jviktes/Astrograf/3DPrint/Modular_planetary_gearbox__1024/images/3fe68c79d25a81dcb26cbcb582fad782_preview_featured.jpg

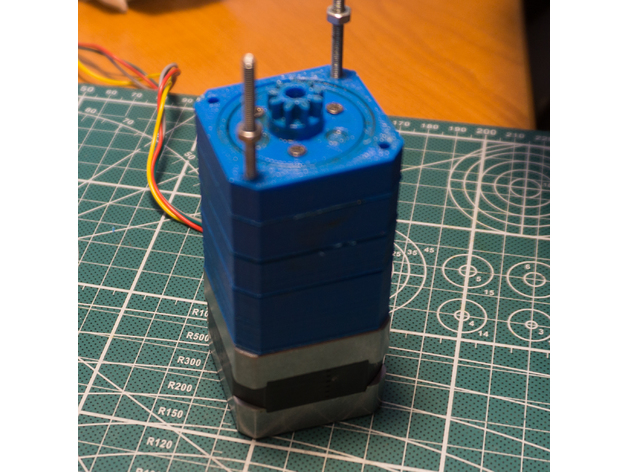
3DPrint/Modular_planetary_gearbox__1024/images/3fe68c79d25a81dcb26cbcb582fad782_preview_featured.jpg
