jviktes/Astrograf/3DPrint/Modular_planetary_gearbox__1024/images/6f2f0f552271744cae626b99cfb380dd_preview_featured.jpg

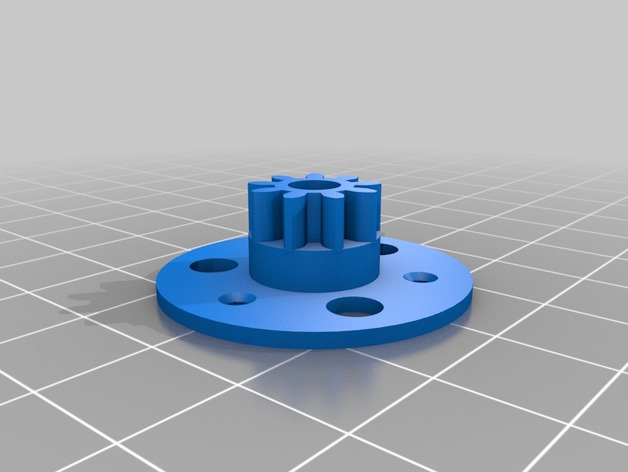
3DPrint/Modular_planetary_gearbox__1024/images/6f2f0f552271744cae626b99cfb380dd_preview_featured.jpg
