jviktes/Astrograf/3DPrint/Modular_planetary_gearbox__1024/images/7bb7e70e9617966f21e6dd5f7fba5066_preview_featured.jpg

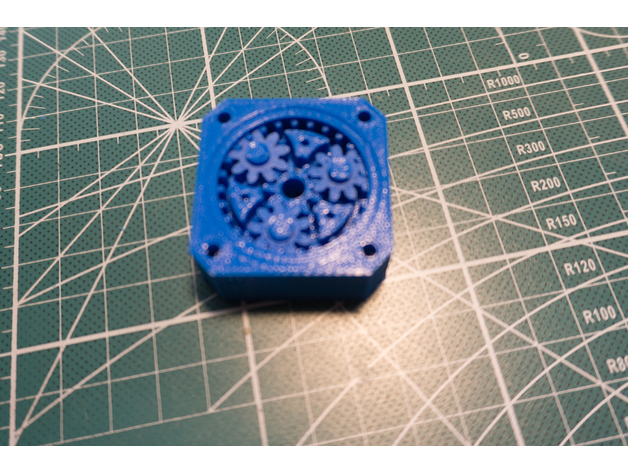
3DPrint/Modular_planetary_gearbox__1024/images/7bb7e70e9617966f21e6dd5f7fba5066_preview_featured.jpg
