jviktes/Astrograf/3DPrint/Modular_planetary_gearbox__1024/images/9a64f82b3e09b2cae3e578f5d89d99b6_preview_featured.jpg

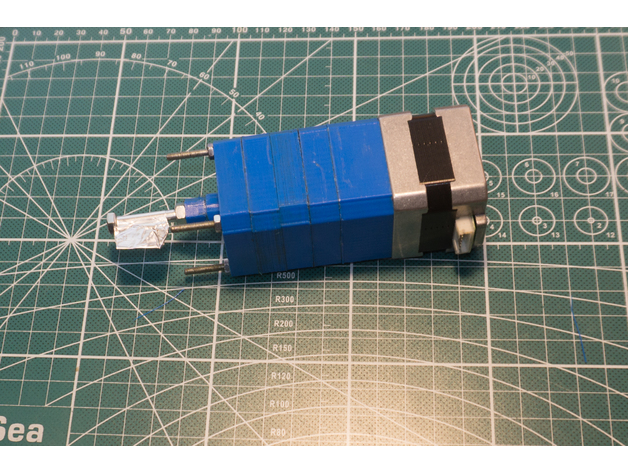
3DPrint/Modular_planetary_gearbox__1024/images/9a64f82b3e09b2cae3e578f5d89d99b6_preview_featured.jpg
