jviktes/Astrograf/3DPrint/Modular_planetary_gearbox__1024/images/9c8101880a9e5dfc09dd12966d4b34e6_preview_featured.jpg

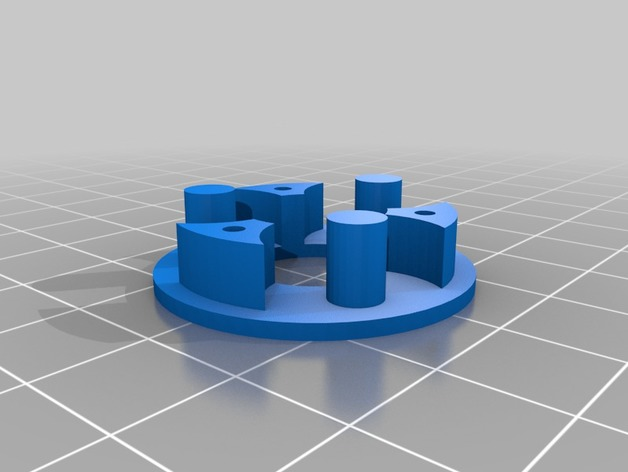
3DPrint/Modular_planetary_gearbox__1024/images/9c8101880a9e5dfc09dd12966d4b34e6_preview_featured.jpg
