jviktes/Astrograf/3DPrint/Modular_planetary_gearbox__1024/images/43a152fd7e8cf67ea3baf1d21f4f2fe9_preview_featured.jpg

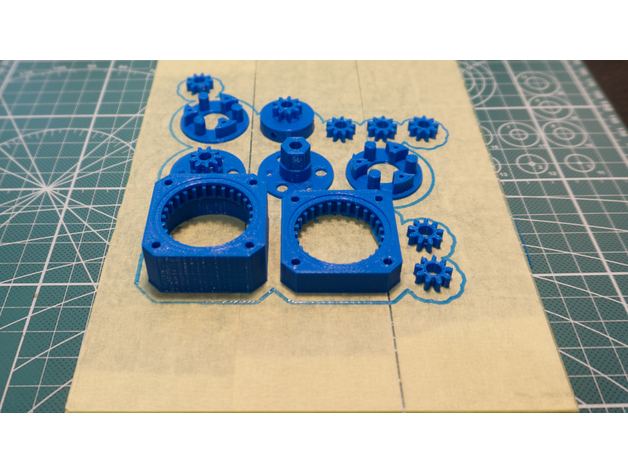
3DPrint/Modular_planetary_gearbox__1024/images/43a152fd7e8cf67ea3baf1d21f4f2fe9_preview_featured.jpg
