jviktes/Astrograf/3DPrint/Modular_planetary_gearbox__1024/images/76d2ecaf834df607a9b20ee27e41b75c_preview_featured.jpg

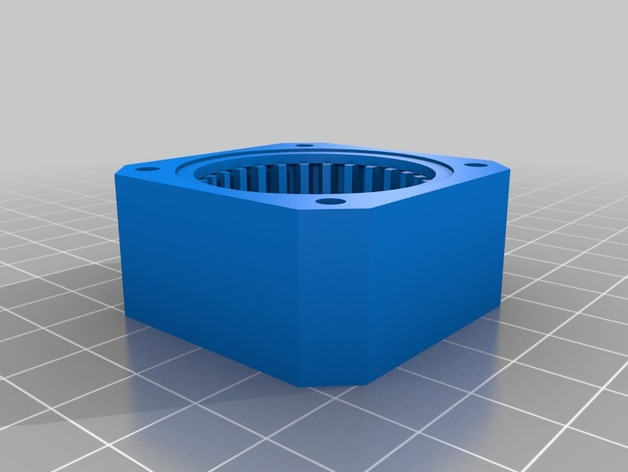
3DPrint/Modular_planetary_gearbox__1024/images/76d2ecaf834df607a9b20ee27e41b75c_preview_featured.jpg
