jviktes/Astrograf/3DPrint/Modular_planetary_gearbox__1024/images/174da9a083a57a64a7c0f3720b108f7d_preview_featured.jpg

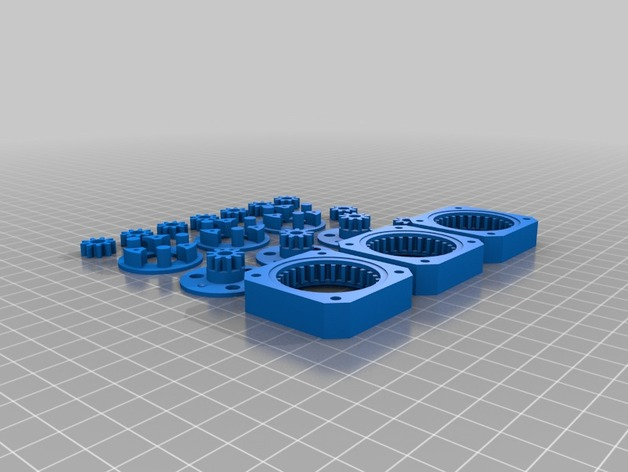
3DPrint/Modular_planetary_gearbox__1024/images/174da9a083a57a64a7c0f3720b108f7d_preview_featured.jpg
