jviktes/Astrograf/3DPrint/Modular_planetary_gearbox__1024/images/953fd65dd4ddc953e1353cae30e27056_preview_featured.jpg

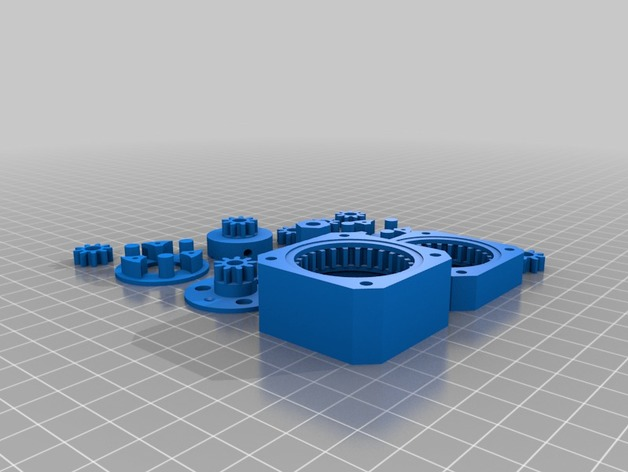
3DPrint/Modular_planetary_gearbox__1024/images/953fd65dd4ddc953e1353cae30e27056_preview_featured.jpg
