jviktes/Astrograf/3DPrint/Modular_planetary_gearbox__1024/images/1248a75d7ca7d012274662f457cd7e67_preview_featured.jpg

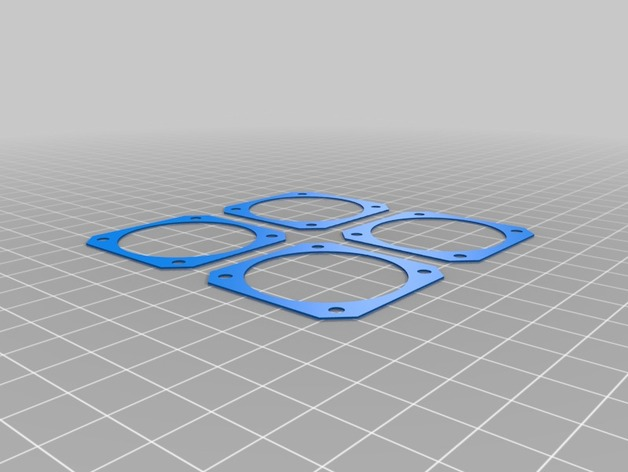
3DPrint/Modular_planetary_gearbox__1024/images/1248a75d7ca7d012274662f457cd7e67_preview_featured.jpg
