jviktes/Astrograf/3DPrint/Modular_planetary_gearbox__1024/images/2090c801b86e893f7edfd4ea6fee8e63_preview_featured.jpg

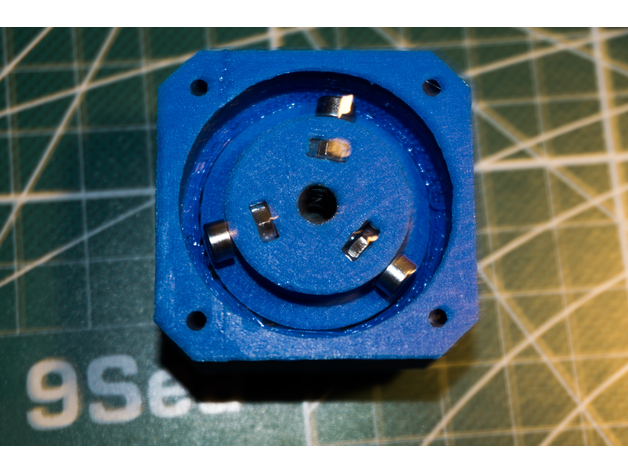
3DPrint/Modular_planetary_gearbox__1024/images/2090c801b86e893f7edfd4ea6fee8e63_preview_featured.jpg
