jviktes/Astrograf/3DPrint/Modular_planetary_gearbox__1024/images/57567420b3f128584251f2cdd674a608_preview_featured.jpg

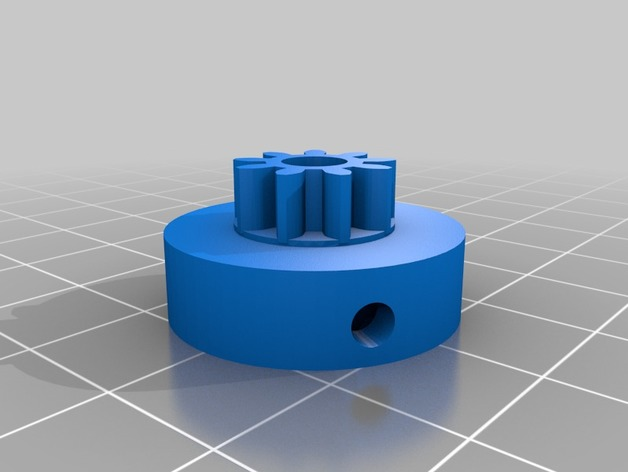
3DPrint/Modular_planetary_gearbox__1024/images/57567420b3f128584251f2cdd674a608_preview_featured.jpg
