jviktes/Astrograf/3DPrint/Modular_planetary_gearbox__1024/images/d7afa6ae71f1685b77fa689912598927_preview_featured.jpg

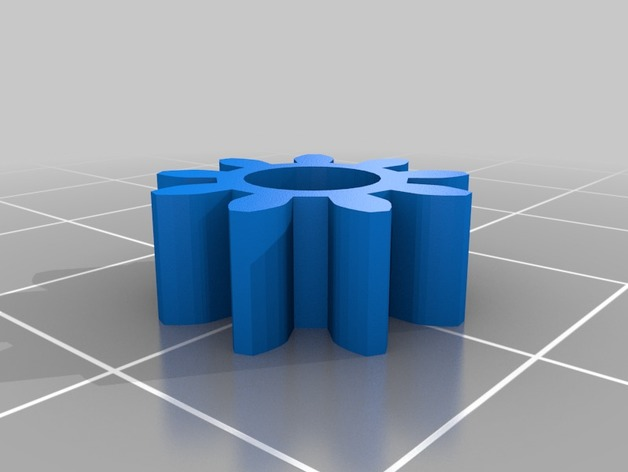
3DPrint/Modular_planetary_gearbox__1024/images/d7afa6ae71f1685b77fa689912598927_preview_featured.jpg
