jviktes/Astrograf/3DPrint/Modular_planetary_gearbox__1024/images/d75aef89d14b9a6239688a6142246159_preview_featured.jpg

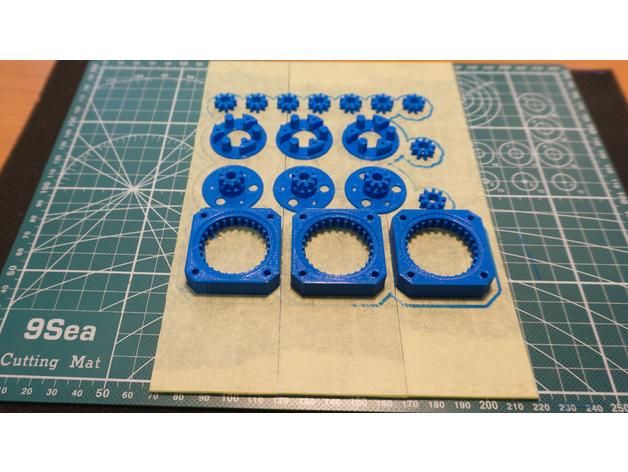
3DPrint/Modular_planetary_gearbox__1024/images/d75aef89d14b9a6239688a6142246159_preview_featured.jpg
