jviktes/Astrograf/3DPrint/Nema_17_holder/images/0cdeb484a66ffd8b90530e48ac5713e8_preview_featured.jpg

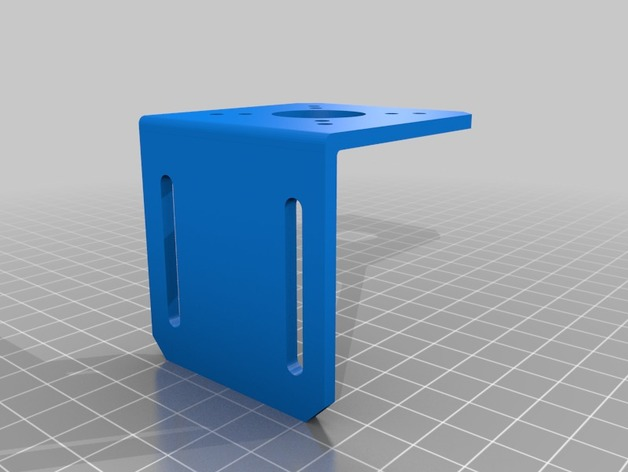
3DPrint/Nema_17_holder/images/0cdeb484a66ffd8b90530e48ac5713e8_preview_featured.jpg
