jviktes/Astrograf/3DPrint/Telescope3D/Images/2021-07-13 14_11_04-.png

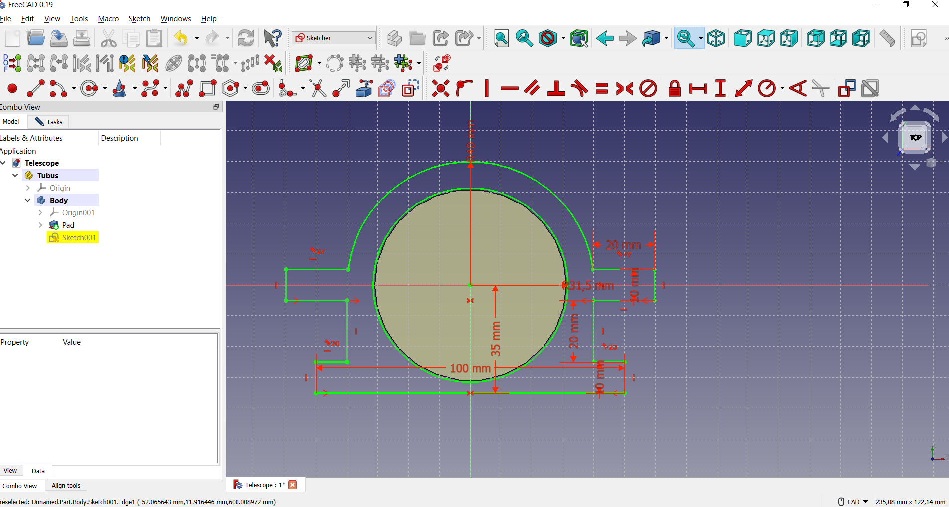
3DPrint/Telescope3D/Images/2021-07-13 14_11_04-.png
