jviktes/Astrograf/AstroCalc/Images/2021-06-29 20_46_09-.png

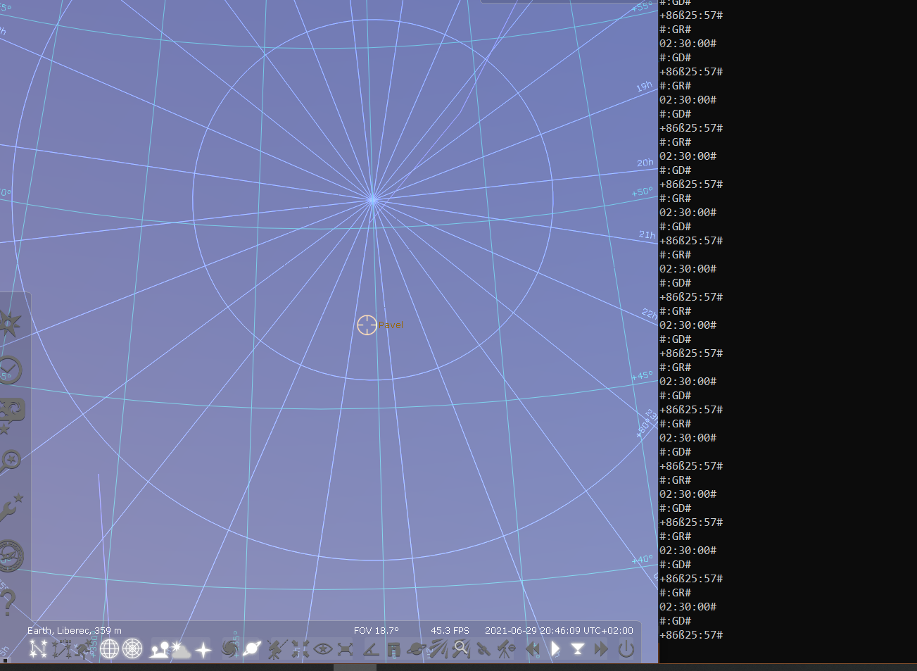
AstroCalc/Images/2021-06-29 20_46_09-.png
