jviktes/Astrograf/AstroCalc/Images/2021-07-05 20_32_24-Stellarium 0.21.0.png

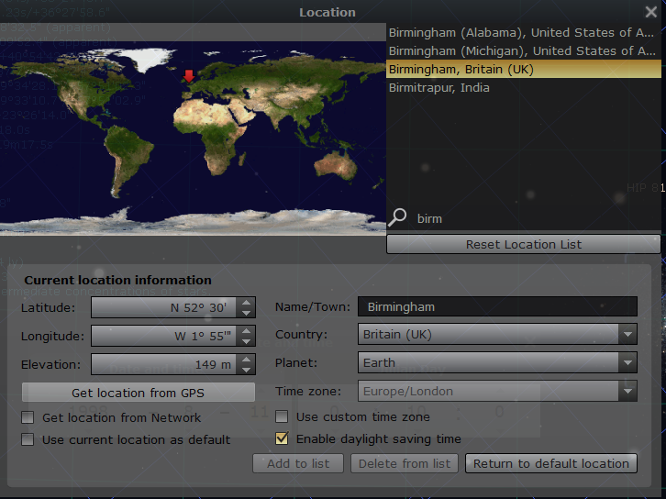
AstroCalc/Images/2021-07-05 20_32_24-Stellarium 0.21.0.png
