jviktes/Astrograf/AstroCalc/Images/2021-07-24 21_46_27-Stellarium 0.21.0.png

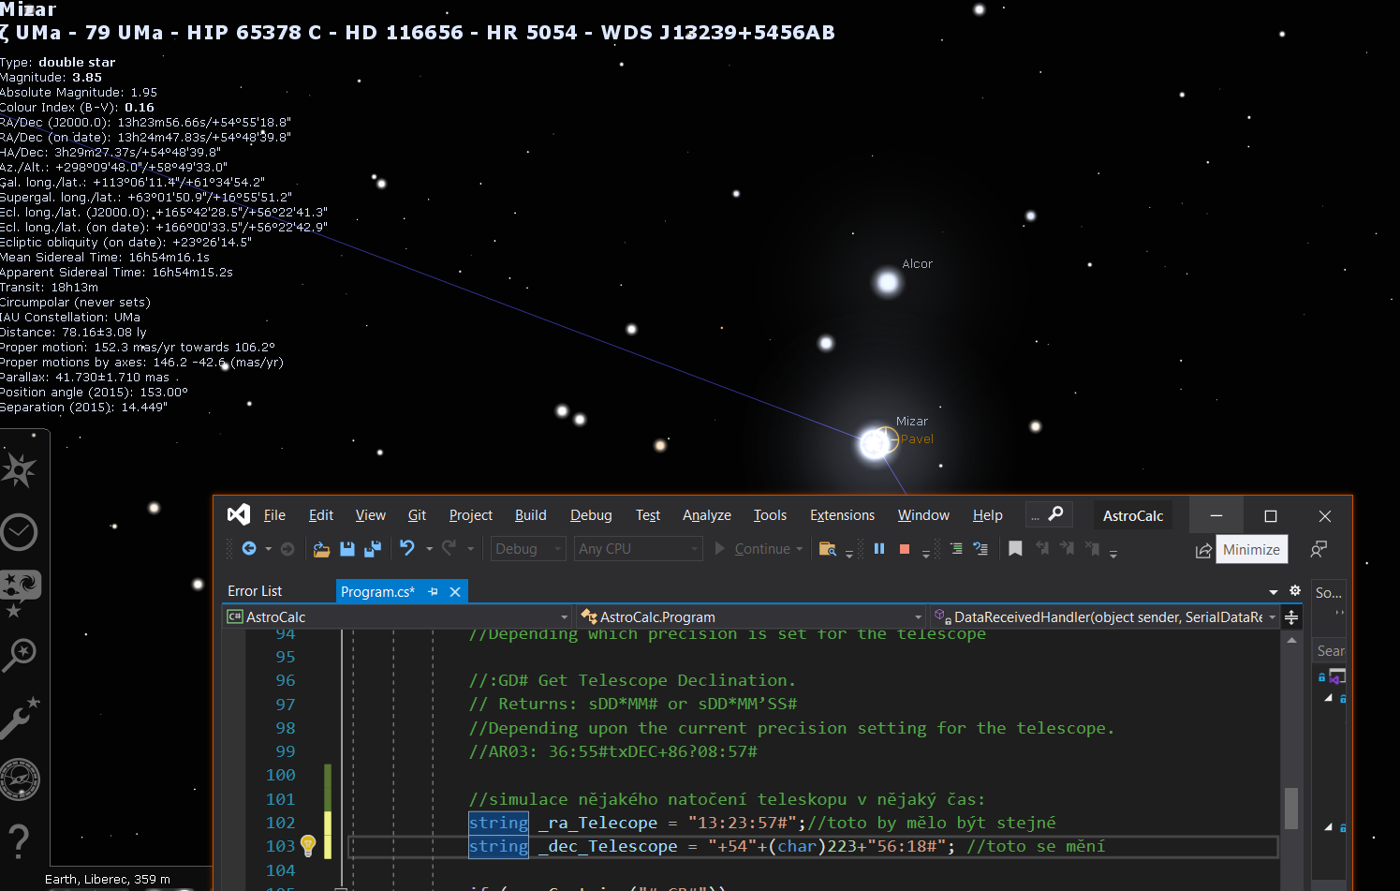
AstroCalc/Images/2021-07-24 21_46_27-Stellarium 0.21.0.png
