jviktes/Astrograf/Montaze/Wiki/8 inch on deck.jpg

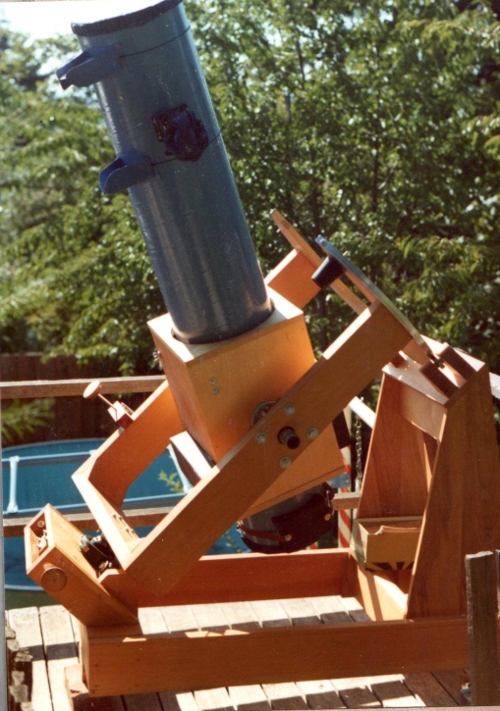
Montaze/Wiki/8 inch on deck.jpg
