jviktes/Astrograf/Montaze/Wiki/b3a265691e6abf68f2a1974e4d472e9f.jpg

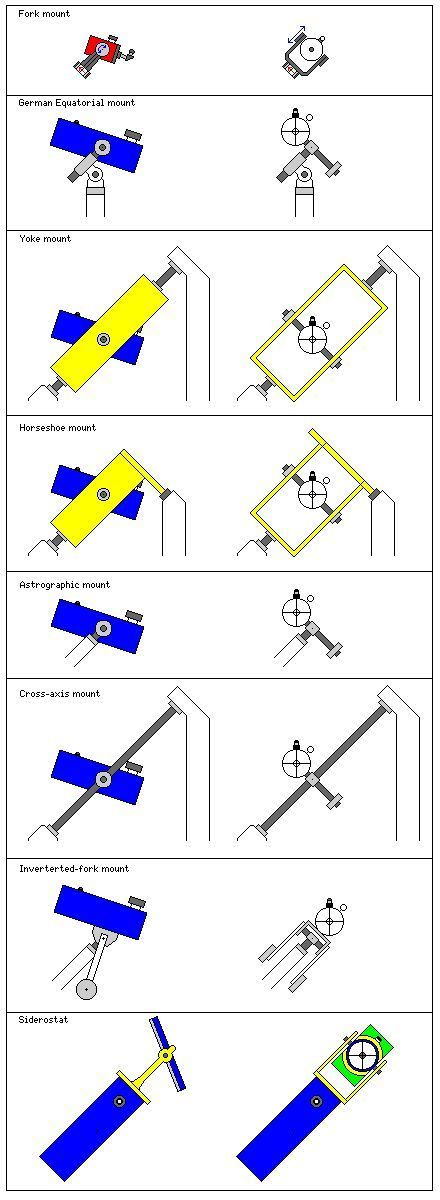
Montaze/Wiki/b3a265691e6abf68f2a1974e4d472e9f.jpg
