jviktes/Astrograf/Montaze/Wiki/F0H9ULFKI4KC9ZJ.jpg

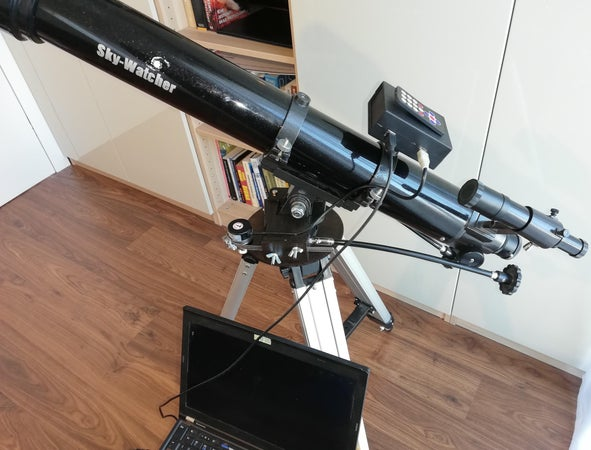
Montaze/Wiki/F0H9ULFKI4KC9ZJ.jpg
