jviktes/Astrograf/Photos/2021-07-07 10_11_59-Window.png

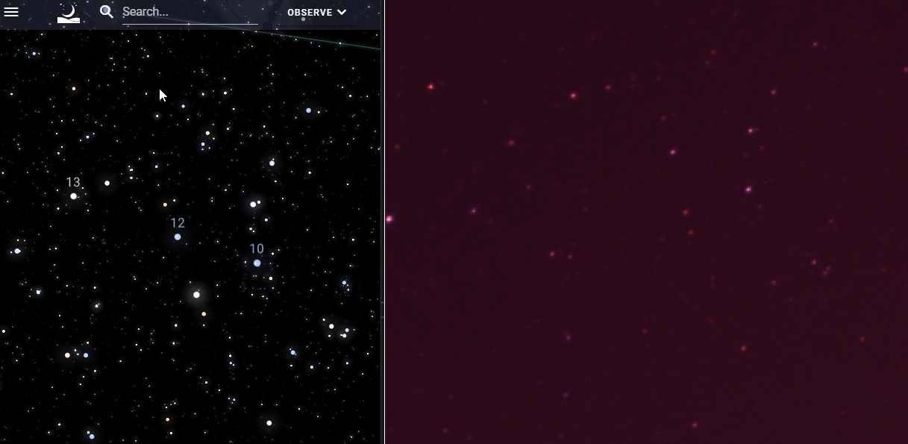
Photos/2021-07-07 10_11_59-Window.png
