jviktes/Astrograf/Photos/2021-07-07 10_25_01-Window.png

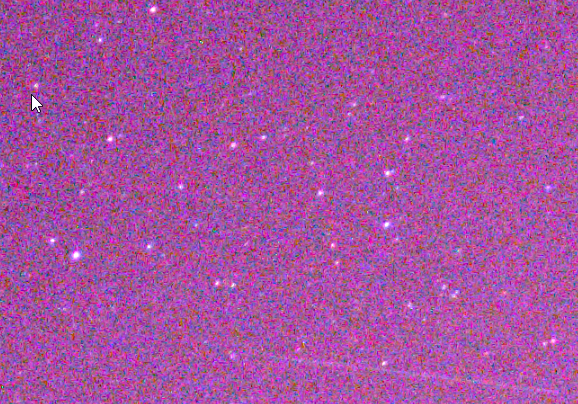
Photos/2021-07-07 10_25_01-Window.png
