jviktes/Astrograf/Photos/2021-09-05 17_56_52-al_az.png

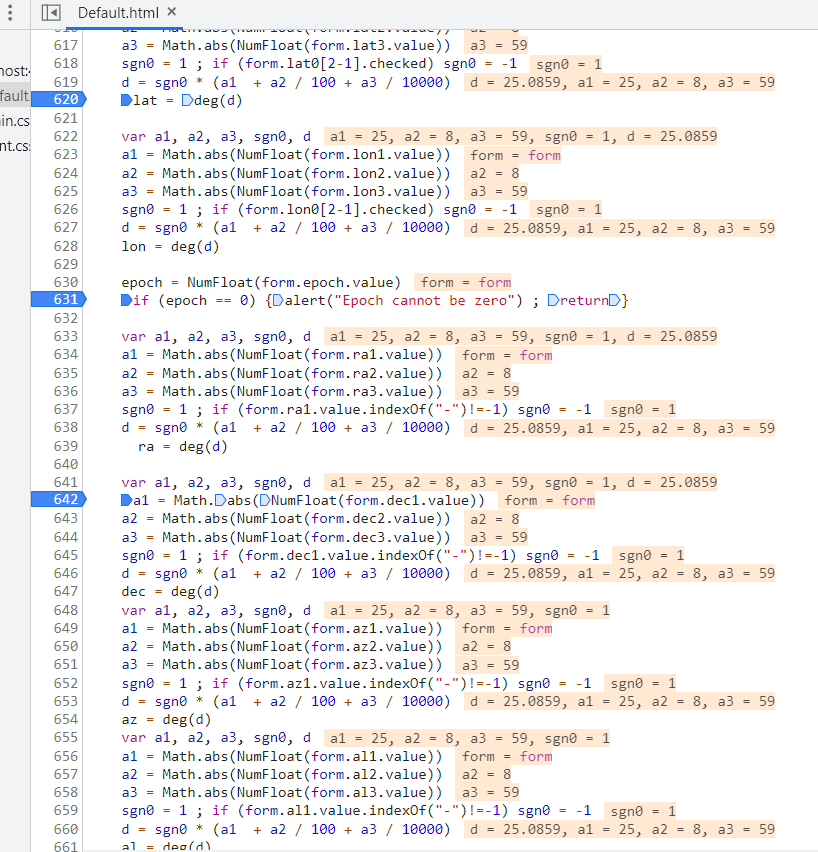
Photos/2021-09-05 17_56_52-al_az.png
