jviktes/Astrograf/Photos/2021-09-05 19_19_43-al_az.png

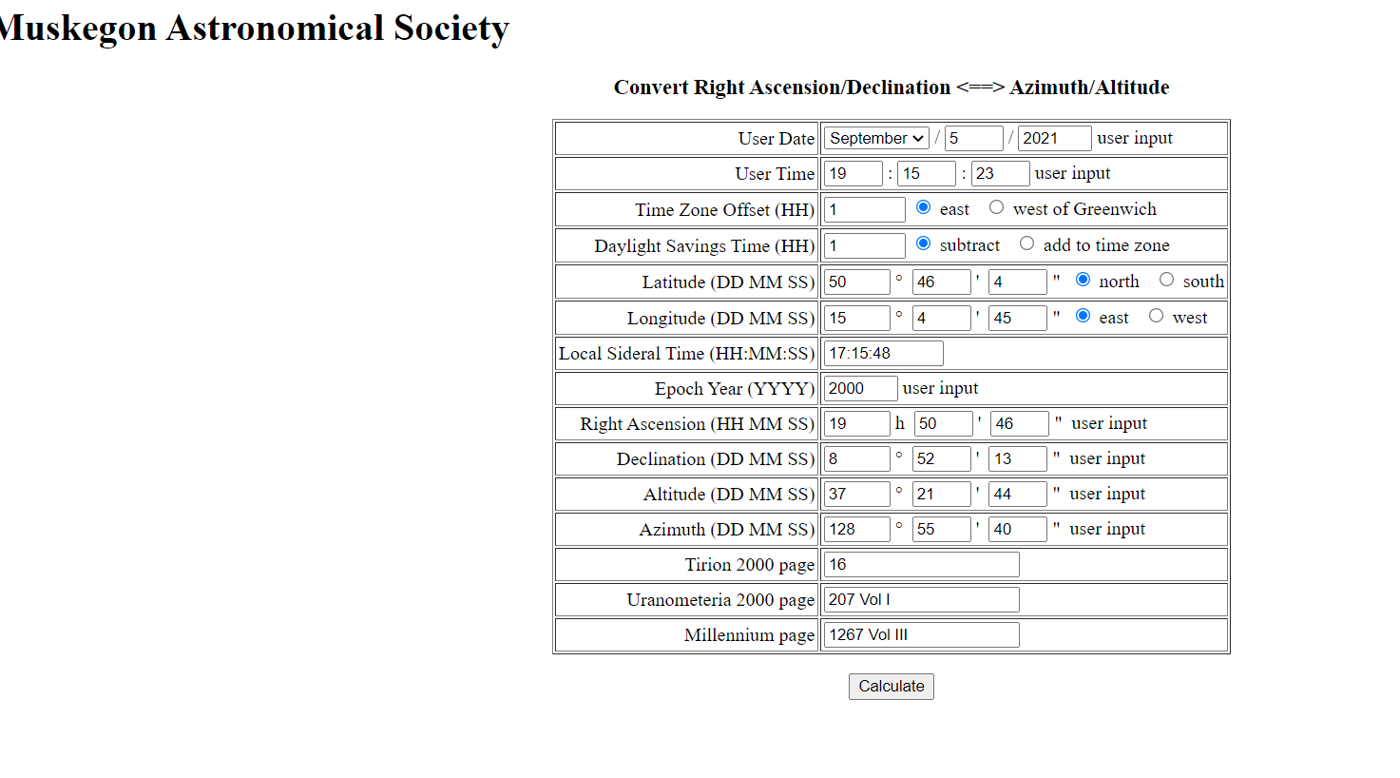
Photos/2021-09-05 19_19_43-al_az.png
