jviktes/Astrograf/Photos/2021-09-10 21_18_42-.png

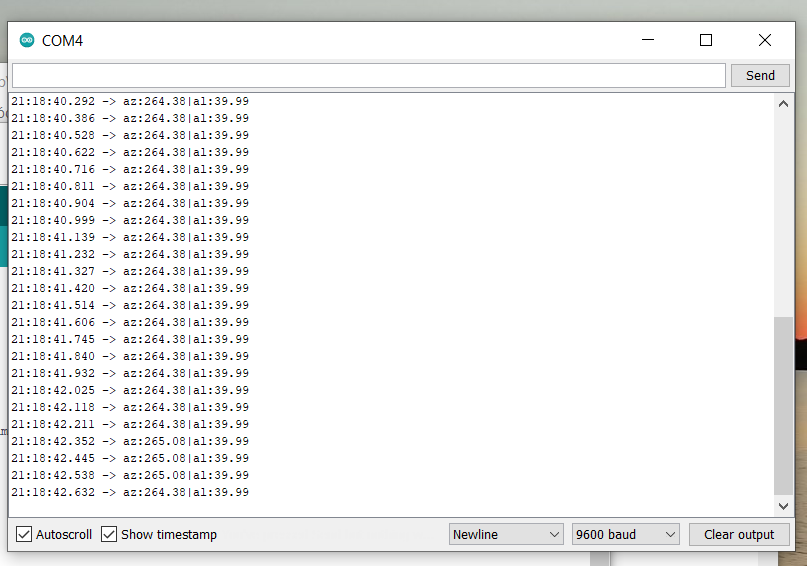
Photos/2021-09-10 21_18_42-.png
