jviktes/Astrograf/Photos/2021-09-10 21_22_01-.png

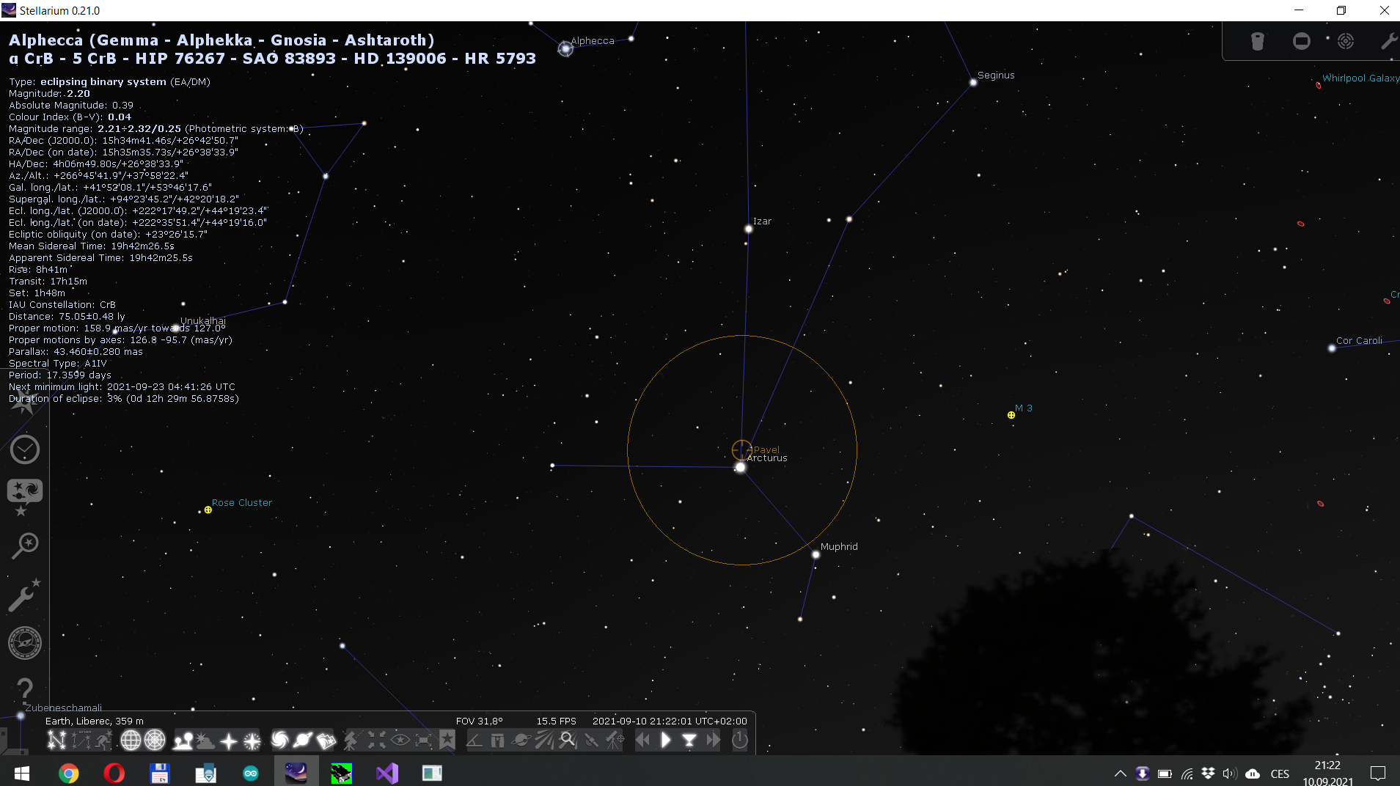
Photos/2021-09-10 21_22_01-.png
