jviktes/Astrograf/Photos/IMG20210526182509.jpg

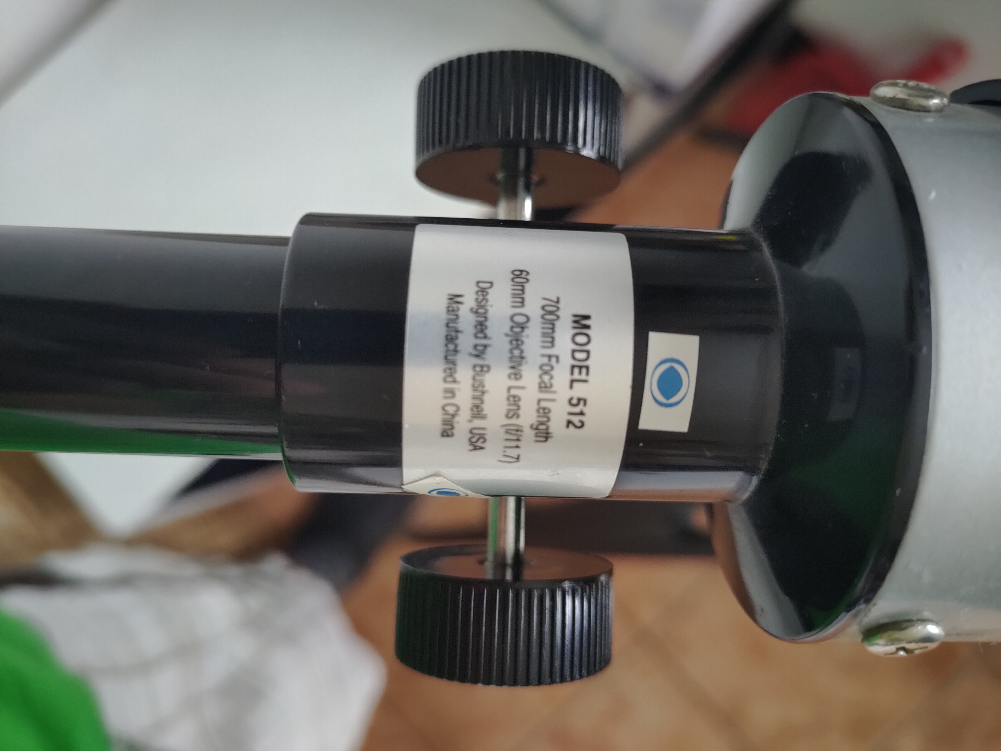
Photos/IMG20210526182509.jpg
