jviktes/Astrograf/Photos/IMG20210610182039.jpg

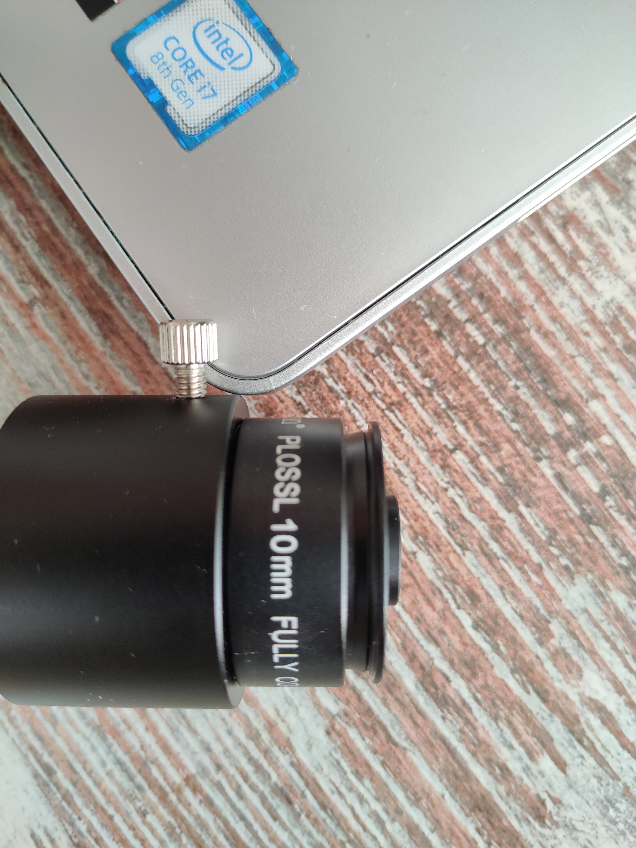
Photos/IMG20210610182039.jpg
