jviktes/Astrograf/Photos/IMG20210910212639.jpg

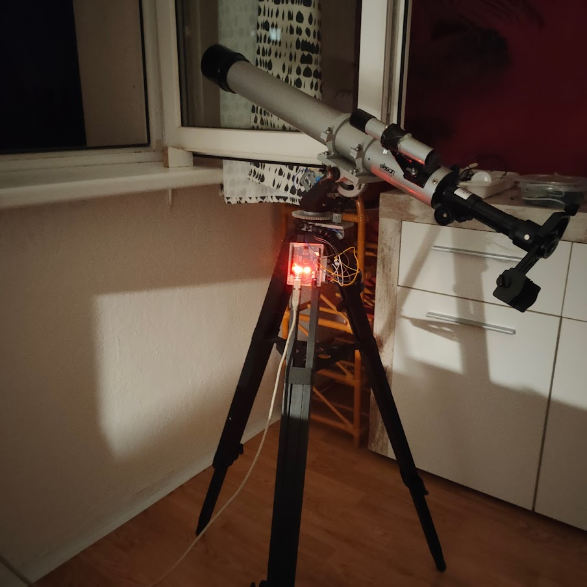
Photos/IMG20210910212639.jpg
