jviktes/Astrograf/Photos/IMG20210910212649.jpg

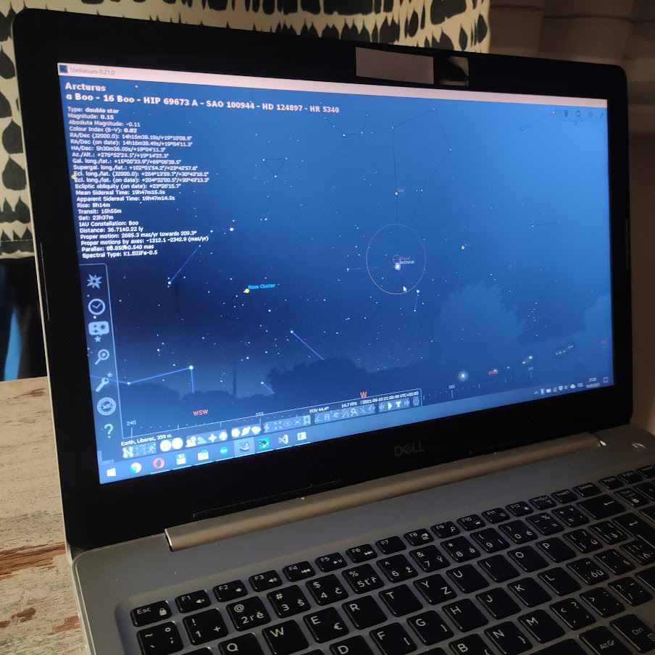
Photos/IMG20210910212649.jpg
