jviktes/Astrograf/Photos/IMG20210910212733.jpg

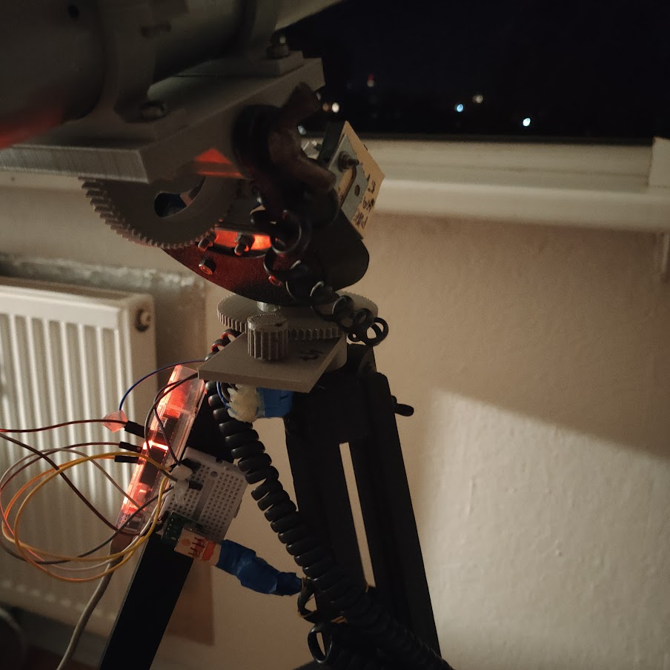
Photos/IMG20210910212733.jpg
