jviktes/Astrograf/3DPrint/Models/new_vzpera1.FCStd

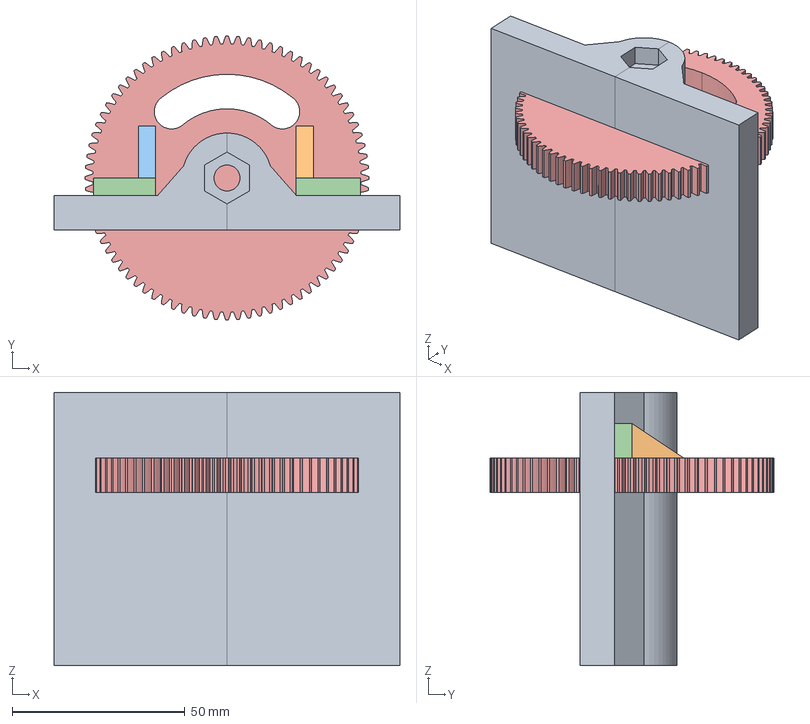
[picture p63: CAD file, 2021-08-28]
3DPrint/Models/new_vzpera1.FCStd
100.0 x 82.0 x 79.0 mm
Podpera001
Podpera
