jviktes/Astrograf/3DPrint/Modular_planetary_gearbox__1024/files/print_part_I_v1.stl

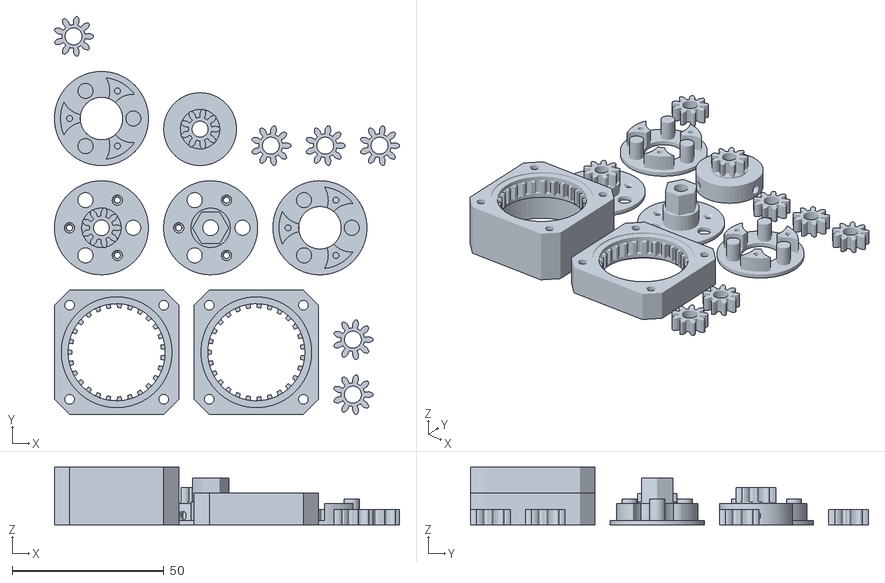
[picture p64: CAD file, 2021-09-24]
3DPrint/Modular_planetary_gearbox__1024/files/print_part_I_v1.stl
113.7 x 131.1 x 19.0
