jviktes/Astrograf/DSLR/3D_models/Zrcadlovka_Ozubena_kola_2_zavitova_hridel.FCStd

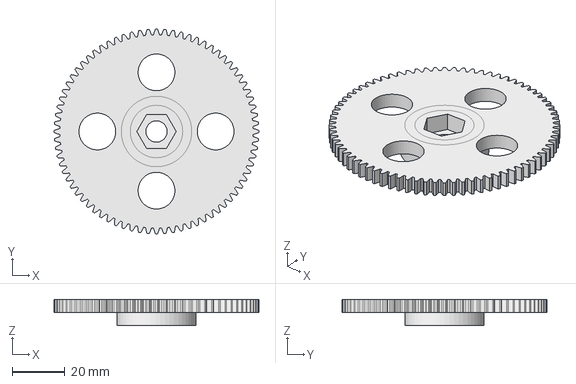
[picture p65: CAD file, 2021-10-20]
DSLR/3D_models/Zrcadlovka_Ozubena_kola_2_zavitova_hridel.FCStd
78.0 x 78.0 x 10.0 mm
