jviktes/Astrograf/3DPrint/Models/tisk/ozub_kolo_potenciometre.stl

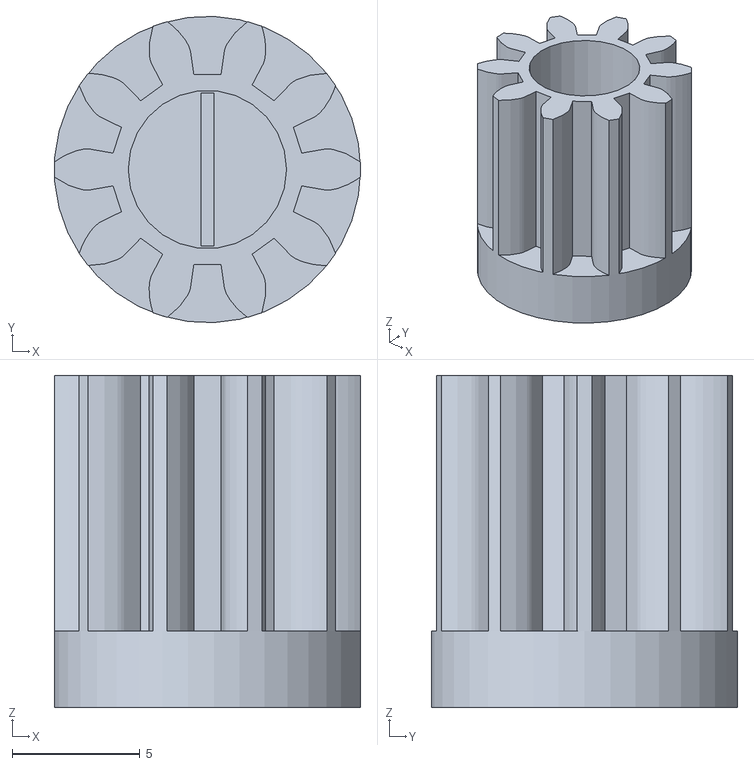
[picture p66: CAD file, 2021-08-30]
3DPrint/Models/tisk/ozub_kolo_potenciometre.stl
12.0 x 12.0 x 13.0
