jviktes/Astrograf/3DPrint/Modular_planetary_gearbox__1024/files/body_I_v1.stl

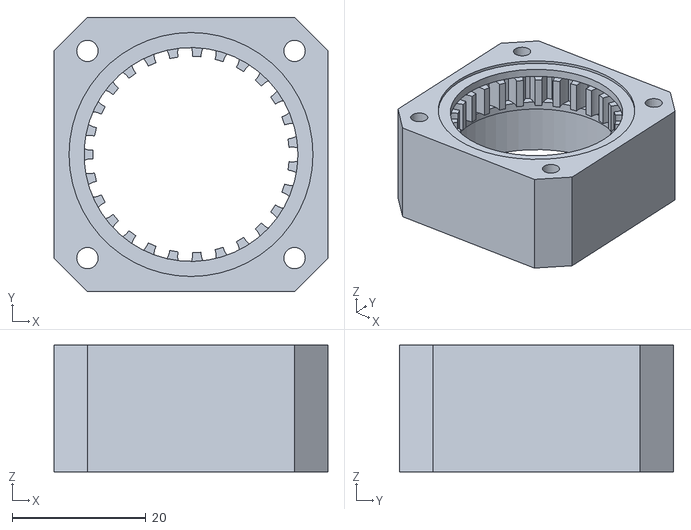
[picture p68: CAD file, 2021-09-24]
3DPrint/Modular_planetary_gearbox__1024/files/body_I_v1.stl
41.0 x 41.0 x 19.0
