jviktes/Astrograf/DSLR/3D_models/Zrcadlovka_Ozubena_kola.FCStd

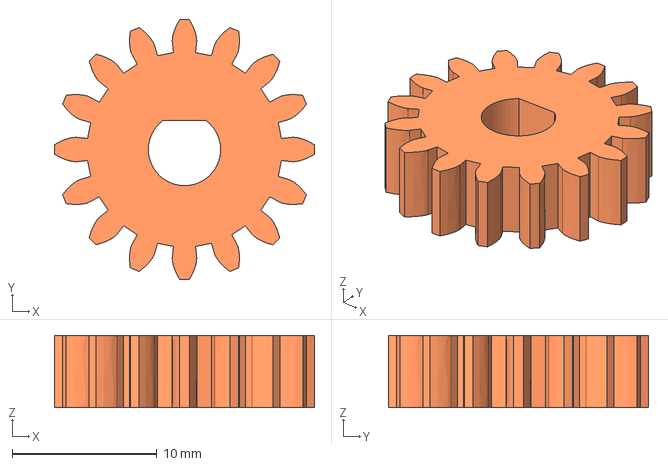
[picture p69: CAD file, 2021-10-05]
DSLR/3D_models/Zrcadlovka_Ozubena_kola.FCStd
18.0 x 18.0 x 5.00 mm
