jviktes/Astrograf/3DPrint/Modular_planetary_gearbox__1024/files/sun_gea_II_v1.stl

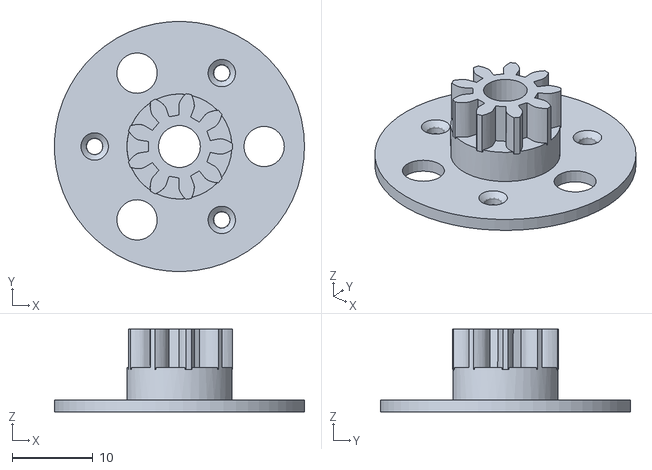
[picture p70: CAD file, 2021-09-24]
3DPrint/Modular_planetary_gearbox__1024/files/sun_gea_II_v1.stl
31.0 x 31.0 x 10.2
