jviktes/Astrograf/DSLR/3D_models/_backUp/hlinikovy_profil-KoncovkaALProfilu.stl

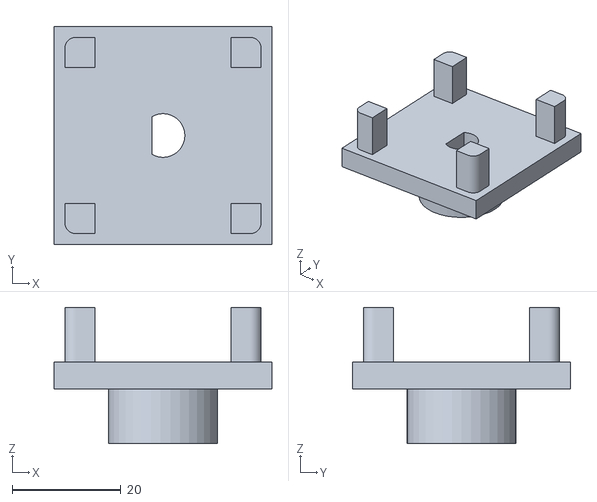
[picture p71: CAD file, 2021-10-05]
DSLR/3D_models/_backUp/hlinikovy_profil-KoncovkaALProfilu.stl
40.0 x 40.0 x 25.0
