jviktes/Astrograf/3DPrint/Modular_planetary_gearbox__1024/files/print_part_II_v1.stl

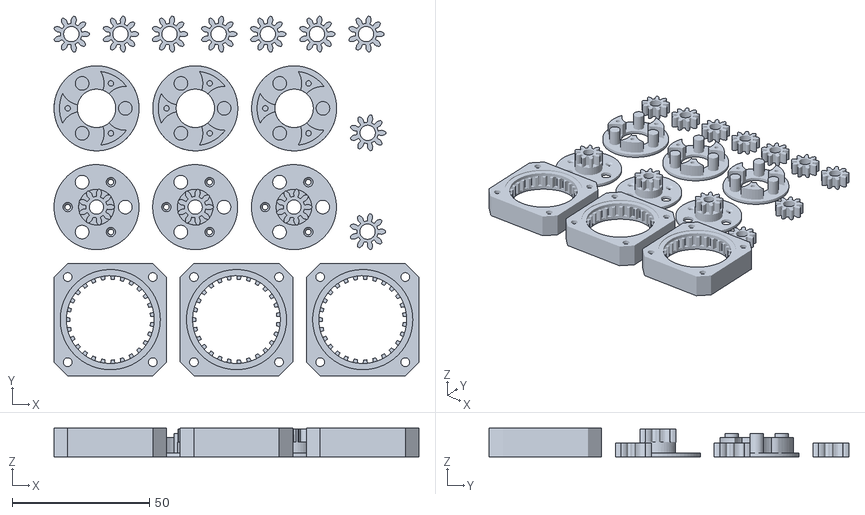
[picture p72: CAD file, 2021-09-24]
3DPrint/Modular_planetary_gearbox__1024/files/print_part_II_v1.stl
133.0 x 131.1 x 10.5
