jviktes/Astrograf/3DPrint/Models/tisk/objimka_2.stl

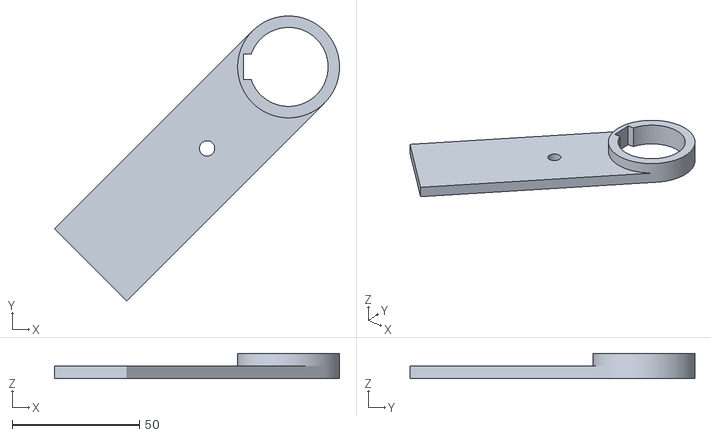
[picture p73: CAD file, 2021-08-23]
3DPrint/Models/tisk/objimka_2.stl
111.9 x 111.9 x 10.0
