jviktes/Astrograf/3DPrint/Modular_planetary_gearbox__1024/files/sun_gear_I_v1.stl

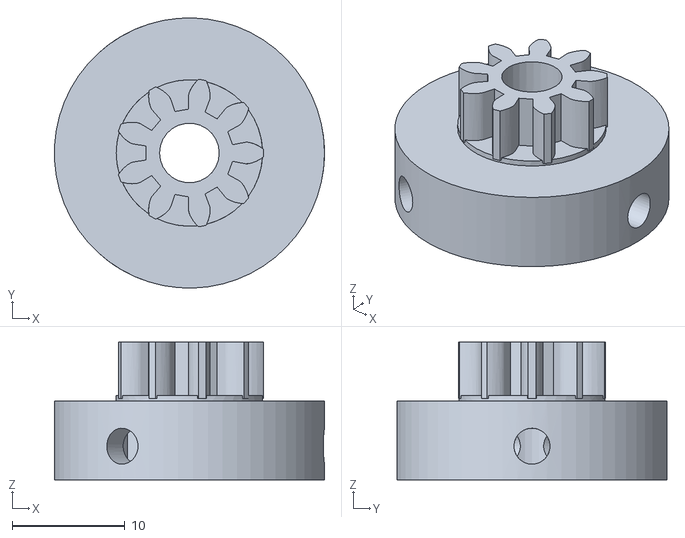
[picture p74: CAD file, 2021-09-24]
3DPrint/Modular_planetary_gearbox__1024/files/sun_gear_I_v1.stl
24.0 x 24.0 x 12.2
