jviktes/Astrograf/3DPrint/Models/tisk/drzak.stl

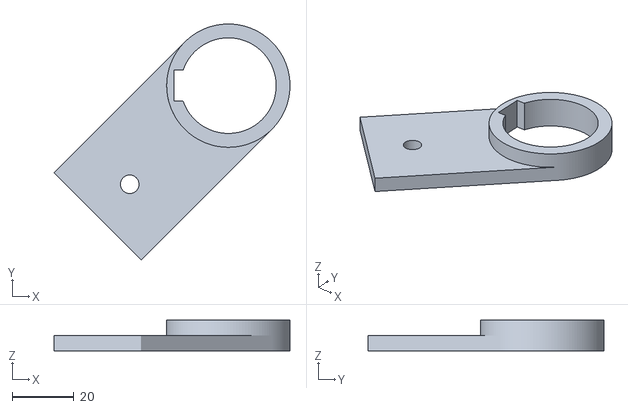
[picture p75: CAD file, 2021-08-23]
3DPrint/Models/tisk/drzak.stl
76.6 x 76.6 x 10.0
