jviktes/Astrograf/3DPrint/Models/tisk/objimka.stl

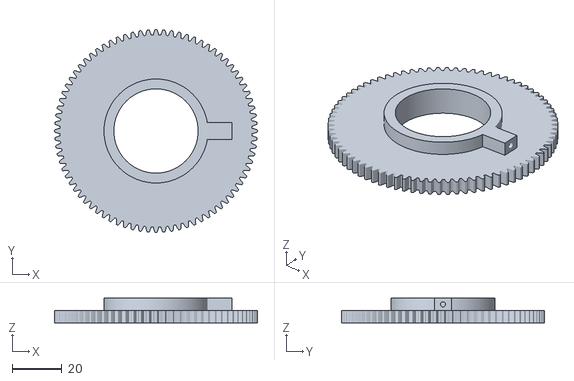
[picture p77: CAD file, 2021-08-23]
3DPrint/Models/tisk/objimka.stl
82.0 x 82.0 x 10.0
