jviktes/Astrograf/3DPrint/Models/tisk/azimut_mount-Male_ozub_kolo.stl

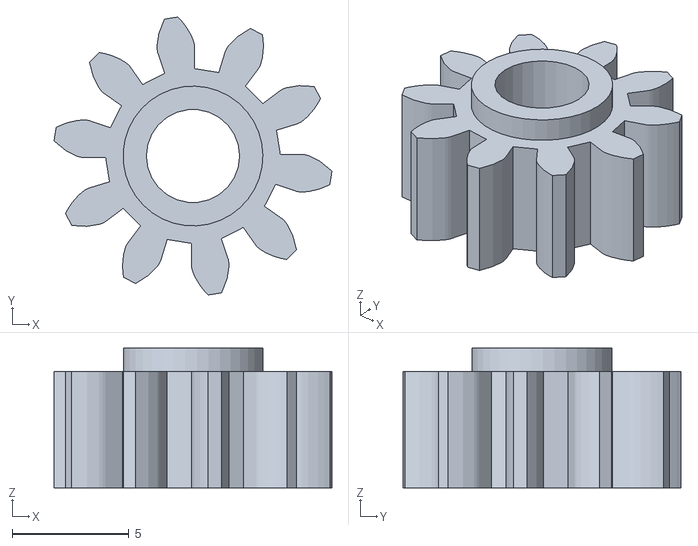
[picture p78: CAD file, 2021-08-23]
3DPrint/Models/tisk/azimut_mount-Male_ozub_kolo.stl
11.9 x 11.9 x 6.00
