jviktes/Astrograf/3DPrint/Models/tisk/new_vzpera2.stl

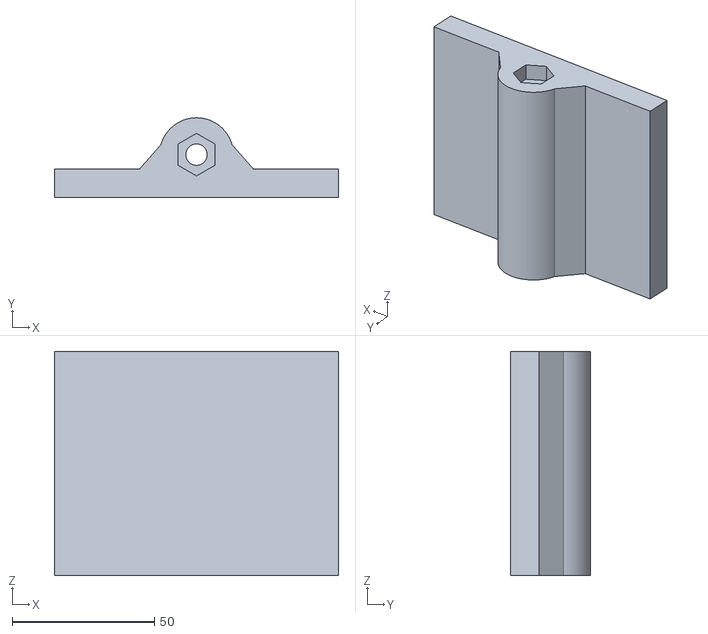
[picture p79: CAD file, 2021-08-11]
3DPrint/Models/tisk/new_vzpera2.stl
100.0 x 28.0 x 79.0
