jviktes/Astrograf/DisplayAzimut/DisplayAzimut.ino

#include <Wire.h>
#include <Adafruit_Sensor.h>
#include <Adafruit_LSM303_U.h>
#include <Adafruit_9DOF.h>
#include <Adafruit_L3GD20_U.h>

#include <LiquidCrystal_I2C.h>

/* Assign a unique ID to the sensors */
Adafruit_9DOF                 dof   = Adafruit_9DOF();
Adafruit_LSM303_Accel_Unified accel = Adafruit_LSM303_Accel_Unified(30301);
Adafruit_LSM303_Mag_Unified   mag   = Adafruit_LSM303_Mag_Unified(30302);

LiquidCrystal_I2C lcd(0x27,16,2);  // set the LCD address to 0x3F for a 16 chars and 2 line display


/**************************************************************************/
/*!
    @brief  Initialises all the sensors used by this example
*/
/**************************************************************************/
void initSensors()
{
  if(!accel.begin())
  {
    /* There was a problem detecting the LSM303 ... check your connections */
    Serial.println(F("Ooops, no LSM303 detected ... Check your wiring!"));
    while(1);
  }
  if(!mag.begin())
  {
    /* There was a problem detecting the LSM303 ... check your connections */
    Serial.println("Ooops, no LSM303 detected ... Check your wiring!");
    while(1);
  }
}

/**************************************************************************/
/*!

*/
/**************************************************************************/
void setup(void)
{
  Serial.begin(115200);
  Serial.println(F("Adafruit 9 DOF Pitch/Roll/Heading Example")); Serial.println("");
  
  /* Initialise the sensors */
  initSensors();

  lcd.init();
  lcd.clear();         
  lcd.backlight();      // Make sure backlight is on
  
  // Print a message on both lines of the LCD.
  lcd.setCursor(2,0);   //Set cursor to character 2 on line 0
  lcd.print("Hello world!");
  
  lcd.setCursor(2,1);   //Move cursor to character 2 on line 1
  lcd.print("LCD Tutorial");
  
}

/**************************************************************************/
/*!
    @brief  Constantly check the roll/pitch/heading/altitude/temperature
*/
/**************************************************************************/
void loop(void)
{
        
  sensors_event_t accel_event;
  sensors_event_t mag_event;
  sensors_vec_t   orientation;

  /* Read the accelerometer and magnetometer */
  accel.getEvent(&accel_event);
  mag.getEvent(&mag_event);

  /* Use the new fusionGetOrientation function to merge accel/mag data */  
  if (dof.fusionGetOrientation(&accel_event, &mag_event, &orientation))
  {
    /* 'orientation' should have valid .roll and .pitch fields */
    Serial.print(F("Orientation: "));
    Serial.print(orientation.roll);
    Serial.print(F(" "));
    Serial.print(orientation.pitch);
    Serial.print(F(" "));
    Serial.print(orientation.heading);
    Serial.println(F(""));
  }

  lcd.setCursor(2,0);   //Set cursor to character 2 on line 0
  lcd.print("V:"+String(orientation.pitch));
  
  lcd.setCursor(2,1);   //Move cursor to character 2 on line 1
  String headingCorrectAngle = "";
  if (orientation.heading<0) {
    headingCorrectAngle = String(orientation.heading*-1);
  }
  else {
    headingCorrectAngle = String(360-orientation.heading);
  }
  
  lcd.print("Az:"+String(headingCorrectAngle)); //ukazuje uhel v minus a obracene proti smeru S-->V atd.

Serial.println("V:"+String(orientation.pitch));
Serial.println("Az:"+String(headingCorrectAngle));
  
  delay(1000);
  lcd.clear();
}
