jviktes/Astrograf/StepMotors/sandbox/stepMotor_A4988/stepMotor_A4988.ino

//test prepisu
// Define pin connections & motor's steps per revolution
const int dirPin = 2;
const int stepPin = 3;
const int stepsPerRevolution = 200;

void setup()
{
  // Declare pins as Outputs
  pinMode(stepPin, OUTPUT);
  pinMode(dirPin, OUTPUT);
  pinMode(6, OUTPUT); //Enable
  digitalWrite(6,LOW);   
  
}
void loop()
{
  // Set motor direction clockwise
  digitalWrite(dirPin, HIGH);

  // Spin motor slowly
  for(int x = 0; x < stepsPerRevolution; x++)
  {
    digitalWrite(stepPin, HIGH);
    delayMicroseconds(2000);
    digitalWrite(stepPin, LOW);
    delayMicroseconds(2000);
  }
  delay(1000); // Wait a second
  
  // Set motor direction counterclockwise
  digitalWrite(dirPin, LOW);

  // Spin motor quickly
  for(int x = 0; x < stepsPerRevolution; x++)
  {
    digitalWrite(stepPin, HIGH);
    delayMicroseconds(1000);
    digitalWrite(stepPin, LOW);
    delayMicroseconds(1000);
  }
  delay(1000); // Wait a second
}
